CherdonFlash/SimpleRemote/mcu/Code/mobile.h

#ifndef _MOBILE_H_
#define _MOBILE_H_

#include "stm32f10x.h"
extern int8_t mobile_1;
extern int8_t mobile_2;
extern int8_t mobile_3;
extern int8_t mobile_4;
void mobile_init(void);
void mobile_data(void);
#endif
