CherdonFlash/SimpleRemote/mcu/Code/oledfont.h

#ifndef __OLEDFONT_H_
#define __OLEDFONT_H_

#include "stm32f10x.h"

const uint8_t zhong[2][16] = {
// "中"
	{0x00,0x00,0xF0,0x10,0x10,0x10,0x10,0xFF,0x10,0x10,0x10,0x10,0xF0,0x00,0x00,0x00},
	{0x00,0x00,0x0F,0x04,0x04,0x04,0x04,0xFF,0x04,0x04,0x04,0x04,0x0F,0x00,0x00,0x00}
    
};
#endif
