CherdonFlash/SimpleRemote/mcu/Code/uart.c

#include "uart.h"

// 初始化 USART1，波特率115200，8N1，无中断
void USART1_Init(uint32_t baudrate)
{
    GPIO_InitTypeDef GPIO_InitStructure;
    USART_InitTypeDef USART_InitStructure;

    // 1. 使能时钟
    RCC_APB2PeriphClockCmd(RCC_APB2Periph_GPIOA | RCC_APB2Periph_USART1, ENABLE);

    // 2. 配置 PA9 为推挽复用输出（TX）
    GPIO_InitStructure.GPIO_Pin = GPIO_Pin_9;
    GPIO_InitStructure.GPIO_Mode = GPIO_Mode_AF_PP;
    GPIO_InitStructure.GPIO_Speed = GPIO_Speed_50MHz;
    GPIO_Init(GPIOA, &GPIO_InitStructure);

    // 3. 配置 PA10 为浮空输入（RX）
    GPIO_InitStructure.GPIO_Pin = GPIO_Pin_10;
    GPIO_InitStructure.GPIO_Mode = GPIO_Mode_IN_FLOATING;
    GPIO_Init(GPIOA, &GPIO_InitStructure);

    // 4. 配置串口参数
    USART_InitStructure.USART_BaudRate = baudrate;
    USART_InitStructure.USART_WordLength = USART_WordLength_8b;
    USART_InitStructure.USART_StopBits = USART_StopBits_1;
    USART_InitStructure.USART_Parity = USART_Parity_No;
    USART_InitStructure.USART_HardwareFlowControl = USART_HardwareFlowControl_None;
    USART_InitStructure.USART_Mode = USART_Mode_Tx | USART_Mode_Rx;
    USART_Init(USART1, &USART_InitStructure);

    // 5. 使能串口
    USART_Cmd(USART1, ENABLE);
}

void UART1_SendChar(uint8_t ch)
{
    USART_SendData(USART1, ch);
    while (USART_GetFlagStatus(USART1, USART_FLAG_TXE) == RESET);
}

void UART1_SendString(const char* str)
{
    while (*str)
    {
        UART1_SendChar(*str++);
    }
}

void UART1_Printf(const char *fmt, ...)
{
    char buffer[128];  // 根据需要调整缓冲区大小
    va_list args;
    va_start(args, fmt);
    vsnprintf(buffer, sizeof(buffer), fmt, args);
    va_end(args);

    UART1_SendString(buffer);
}
